LaskaKit/ESP32-C3-LPKit/SW/SH1106_SCD41_ESP32-C3-LPKit/DSEG14_Classic_Bold_12px.h

// Created by http://oleddisplay.squix.ch/ Consider a donation
// In case of problems make sure that you are using the font file with the correct version!
const uint8_t DSEG14_Classic_Bold_12Bitmaps[] PROGMEM = {

	// Bitmap Data:
	0x00, // ' '
	0x00, // '!'
	0xC6,0xF7,0xB8,0x00, // '"'
	0xF9,0x99,0x99,0x99,0xF0, // '#'
	0x7E,0xC0,0xD8,0xD8,0xD8,0xAC,0x2D,0x1B,0x1B,0x1B,0x03,0x7E, // '$'
	0xC0,0xE4,0xE4,0xE4,0xAC,0x2D,0x27,0x27,0x27,0x03, // '%'
	0xFC,0x01,0x22,0x44,0x80,0x00,0xA7,0x4E,0x9C,0x1F,0xE0, // '&'
	0xFC, // '''
	0xE7, // '('
	0xE7, // ')'
	0x79,0xE7,0x96,0x59,0xE7,0x9E, // '*'
	0x30,0xC3,0x16,0x58,0xC3,0x0C, // '+'
	0xE0, // ','
	0x59,0x60, // '-'
	0xC0, // '.'
	0x11,0x10,0x08,0x88, // '/'
	0x7E,0xC3,0xC7,0xC7,0xC7,0x81,0x81,0xE3,0xE3,0xE3,0xC3,0x7E, // '0'
	0xFF,0x5F,0xF0, // '1'
	0x7E,0x03,0x03,0x03,0x03,0x2D,0xAC,0xC0,0xC0,0xC0,0xC0,0x7E, // '2'
	0xFC,0x0C,0x18,0x30,0x6B,0x56,0x83,0x06,0x0C,0x1F,0xE0, // '3'
	0xC3,0xC3,0xC3,0xC3,0xAD,0x2D,0x03,0x03,0x03,0x03, // '4'
	0x7E,0xC0,0xC0,0xC0,0xC0,0xAC,0x2D,0x03,0x03,0x03,0x03,0x7E, // '5'
	0x7E,0xC0,0xC0,0xC0,0xC0,0xAC,0xAD,0xC3,0xC3,0xC3,0xC3,0x7E, // '6'
	0x7E,0xC3,0xC3,0xC3,0xC3,0x81,0x01,0x03,0x03,0x03,0x03, // '7'
	0x7E,0xC3,0xC3,0xC3,0xC3,0xAD,0xAD,0xC3,0xC3,0xC3,0xC3,0x7E, // '8'
	0x7E,0xC3,0xC3,0xC3,0xC3,0xAD,0x2D,0x03,0x03,0x03,0x03,0x7E, // '9'
	0xC0,0x30, // ':'
	0xF9,0x99,0x99,0x99,0xF0, // ';'
	0x08,0x20,0x80,0x01,0x04,0x10,0x03,0xF0, // '<'
	0x59,0x60,0x00,0x00,0x0F,0xC0, // '='
	0x41,0x04,0x00,0x00,0x20,0x82,0x03,0xF0, // '>'
	0x7E,0xC3,0xC3,0xC3,0xC3,0x8D,0x0C,0x18,0x18,0x18, // '?'
	0x7E,0xC3,0xC3,0xC3,0xC3,0x8D,0x8D,0xDB,0xDB,0xDB,0xC3,0x7E, // '@'
	0x7E,0xC3,0xC3,0xC3,0xC3,0xAD,0xAD,0xC3,0xC3,0xC3,0xC3, // 'A'
	0xFC,0x0C,0xD9,0xB3,0x63,0x46,0x9B,0x36,0x6C,0x1F,0xE0, // 'B'
	0x7F,0x83,0x06,0x0C,0x10,0x20,0x60,0xC1,0x83,0x03,0xF0, // 'C'
	0xFC,0x0C,0xD9,0xB3,0x60,0x40,0x9B,0x36,0x6C,0x1F,0xE0, // 'D'
	0x7F,0x83,0x06,0x0C,0x15,0xAB,0x60,0xC1,0x83,0x03,0xF0, // 'E'
	0x7F,0x83,0x06,0x0C,0x15,0xAB,0x60,0xC1,0x83,0x00, // 'F'
	0x7E,0xC0,0xC0,0xC0,0xC0,0x8C,0x8D,0xC3,0xC3,0xC3,0xC3,0x7E, // 'G'
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
};
const GFXglyph DSEG14_Classic_Bold_12Glyphs[] PROGMEM = {
// bitmapOffset, width, height, xAdvance, xOffset, yOffset
	  {     0,   1,   1,   3,    0,   -1 }, // ' '
	  {     1,   1,   1,  11,    0,   -1 }, // '!'
	  {     2,   5,   5,  11,    1,  -11 }, // '"'
	  {     6,   4,   9,   5,    0,   -9 }, // '#'
	  {    11,   8,  12,  11,    1,  -12 }, // '$'
	  {    23,   8,  10,  11,    1,  -11 }, // '%'
	  {    33,   7,  12,  11,    2,  -12 }, // '&'
	  {    44,   2,   4,  11,    4,  -10 }, // '''
	  {    45,   1,   8,  11,    6,  -10 }, // '('
	  {    46,   1,   8,  11,    3,  -10 }, // ')'
	  {    47,   6,   8,  11,    2,  -10 }, // '*'
	  {    53,   6,   8,  11,    2,  -10 }, // '+'
	  {    59,   1,   3,  11,    3,   -5 }, // ','
	  {    60,   6,   2,  11,    2,   -7 }, // '-'
	  {    62,   2,   1,   1,   -1,   -1 }, // '.'
	  {    63,   4,   8,  11,    3,  -10 }, // '/'
	  {    67,   8,  12,  11,    1,  -12 }, // '0'
	  {    79,   2,  10,  11,    7,  -11 }, // '1'
	  {    82,   8,  12,  11,    1,  -12 }, // '2'
	  {    94,   7,  12,  11,    2,  -12 }, // '3'
	  {   105,   8,  10,  11,    1,  -11 }, // '4'
	  {   115,   8,  12,  11,    1,  -12 }, // '5'
	  {   127,   8,  12,  11,    1,  -12 }, // '6'
	  {   139,   8,  11,  11,    1,  -12 }, // '7'
	  {   150,   8,  12,  11,    1,  -12 }, // '8'
	  {   162,   8,  12,  11,    1,  -12 }, // '9'
	  {   174,   2,   6,   3,    0,   -9 }, // ':'
	  {   176,   4,   9,   5,    0,   -9 }, // ';'
	  {   181,   6,  10,  11,    2,  -10 }, // '<'
	  {   189,   6,   7,  11,    2,   -7 }, // '='
	  {   195,   6,  10,  11,    2,  -10 }, // '>'
	  {   203,   8,  10,  11,    1,  -12 }, // '?'
	  {   213,   8,  12,  11,    1,  -12 }, // '@'
	  {   225,   8,  11,  11,    1,  -12 }, // 'A'
	  {   236,   7,  12,  11,    2,  -12 }, // 'B'
	  {   247,   7,  12,  11,    1,  -12 }, // 'C'
	  {   258,   7,  12,  11,    2,  -12 }, // 'D'
	  {   269,   7,  12,  11,    1,  -12 }, // 'E'
	  {   280,   7,  11,  11,    1,  -12 }, // 'F'
	  {   290,   8,  12,  11,    1,  -12 }, // 'G'
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
};
const GFXfont DSEG14_Classic_Bold_12 PROGMEM = {
(uint8_t  *)DSEG14_Classic_Bold_12Bitmaps,(GFXglyph *)DSEG14_Classic_Bold_12Glyphs,0x20, 0x7E, 14};
