LaskaKit/ESP32-C3-LPKit/SW/SH1106_SCD41_ESP32-C3-LPKit/DSEG14_Classic_Bold_32px.h

// Created by http://oleddisplay.squix.ch/ Consider a donation
// In case of problems make sure that you are using the font file with the correct version!
const uint8_t DSEG14_Classic_Bold_32Bitmaps[] PROGMEM = {

	// Bitmap Data:
	0x00, // ' '
	0x00, // '!'
	0x00,0x0C,0x00,0xE0,0x0F,0x00,0xF0,0xFF,0x0F,0xF0,0xFF,0x0F,0xF0,0xFF,0x0F,0xF0,0xFF,0x0F,0xF0,0x6E,0x02,0xC0,0x00, // '"'
	0xFF,0x81,0x81,0x81,0x81,0x81,0x81,0x81,0x81,0x81,0x81,0x81,0x81,0x81,0x81,0x81,0x81,0x81,0x81,0x81,0xFF, // '#'
	0x3F,0xFF,0xC3,0xFF,0xFC,0xDF,0xFF,0x8E,0xFF,0xF0,0xF0,0x00,0x0F,0x0F,0x00,0xF0,0xF0,0x0F,0x0F,0x00,0xF0,0xF0,0x0F,0x0F,0x00,0xF0,0xF0,0x0F,0x0F,0x00,0xF0,0xF0,0x0F,0x06,0x00,0xEF,0xBF,0x0D,0xF9,0xF8,0x1F,0x9F,0xB0,0xFB,0xF7,0x00,0x60,0xF0,0x0F,0x0F,0x00,0xF0,0xF0,0x0F,0x0F,0x00,0xF0,0xF0,0x0F,0x0F,0x00,0xF0,0xF0,0x0F,0x0F,0x00,0xF0,0xF0,0x00,0x0F,0x0F,0xFF,0x71,0xFF,0xFB,0x3F,0xFF,0xC3,0xFF,0xFC, // '$'
	0x00,0x00,0x0C,0x00,0x00,0xE0,0x00,0x0F,0x00,0x00,0xF4,0x02,0x0F,0x60,0x60,0xF6,0x06,0x0F,0x60,0x60,0xF6,0x06,0x0F,0x60,0x60,0xF6,0x06,0x0F,0x20,0x40,0xF0,0x00,0x0E,0xF9,0xF0,0xDF,0x9F,0x81,0xF9,0xFB,0x0F,0x9F,0x70,0x00,0x0F,0x02,0x04,0xF0,0x60,0x6F,0x06,0x06,0xF0,0x60,0x6F,0x06,0x06,0xF0,0x60,0x6F,0x06,0x06,0xF0,0x40,0x2F,0x00,0x00,0xF0,0x00,0x07,0x00,0x00,0x30,0x00,0x00, // '%'
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
	  {  1758,  19,  32,  27,    3,  -32 }, // 'E'
	  {  1834,  19,  31,  27,    3,  -32 }, // 'F'
	  {  1908,  20,  32,  27,    3,  -32 }, // 'G'
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
};
const GFXfont DSEG14_Classic_Bold_32 PROGMEM = {
(uint8_t  *)DSEG14_Classic_Bold_32Bitmaps,(GFXglyph *)DSEG14_Classic_Bold_32Glyphs,0x20, 0x7E, 35};
